alex-ha-192/neo/kicad/buzzers/classic/main/main.kicad_sch

## KiCad design kicad/buzzers/classic/main/main.kicad_sch (2026-09-12)

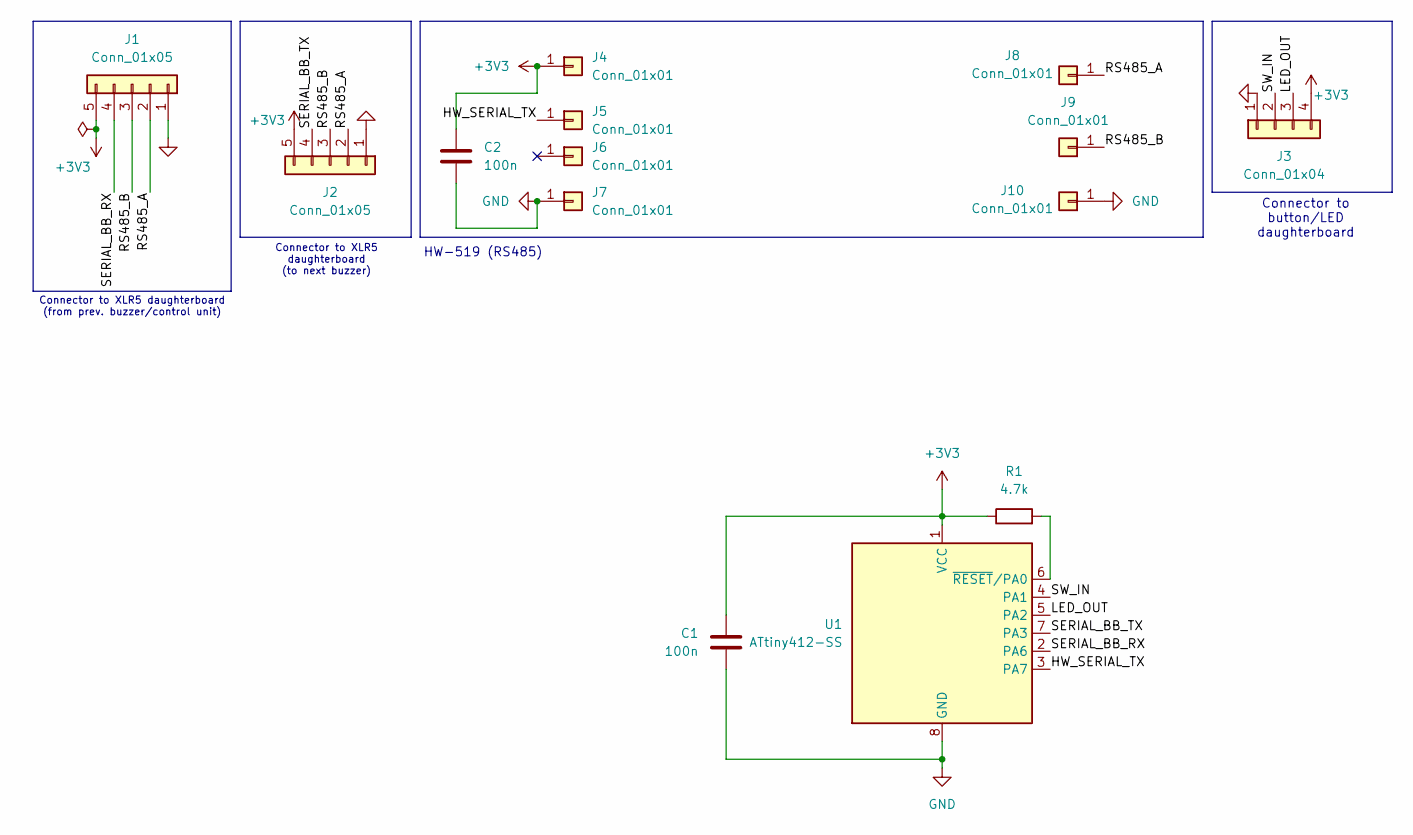
[picture p11: schematic main.kicad_sch]

Parts:
C1, C2: 100n
J1, J2: Conn_01x05
J3: Conn_01x04
J4, J5, J6, J7, J8, J9, J10: Conn_01x01
R1: 4.7k
U1: ATtiny412-SS; SOIC-8_3.9x4.9mm_P1.27mm

Connections:
+3V3: C1.1, C2.1, J1.5, J2.5, J3.4, J4.1, R1.1, U1.1 (VCC)
GND: C1.2, C2.2, J1.1, J2.1, J3.1, J7.1, J10.1, U1.8 (GND)
HW_SERIAL_TX: J5.1, U1.3 (PA7)
LED_OUT: J3.3, U1.5 (PA2)
unnamed: R1.2, U1.6 (~RESET/PA0)
RS485_A: J1.2, J2.2, J8.1
RS485_B: J1.3, J2.3, J9.1
SERIAL_BB_RX: J1.4, U1.2 (PA6)
SERIAL_BB_TX: J2.4, U1.7 (PA3)
SW_IN: J3.2, U1.4 (PA1)

Notes on the sheet:
Connector to button/LED daughterboard
HW-519 (RS485)
Connector to XLR5 daughterboard (from prev. buzzer/control unit)
Connector to XLR5 daughterboard (to next buzzer)
