alex-ha-192/neo/kicad/control_units/classic/led/led.kicad_sch

## KiCad design kicad/control_units/classic/led/led.kicad_sch (2026-06-27)

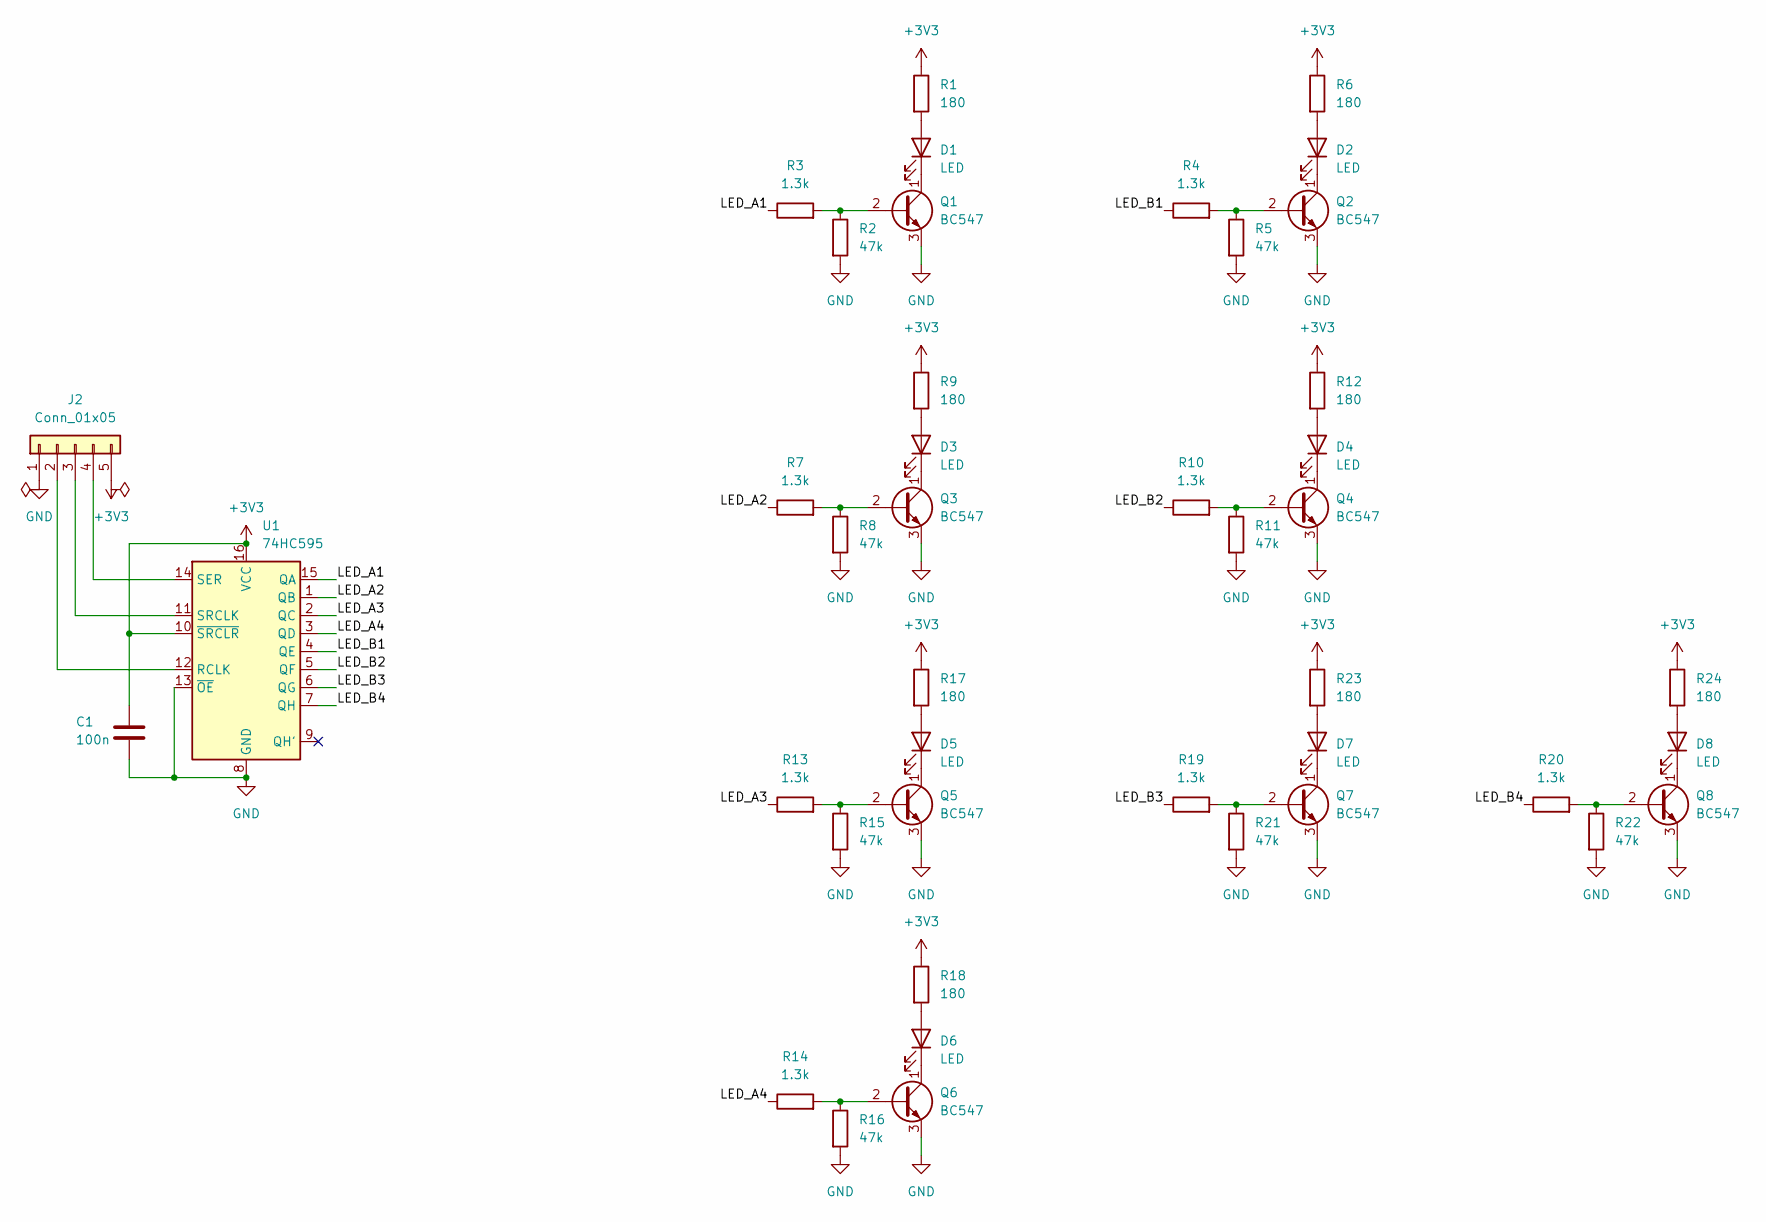
[picture p12: schematic led.kicad_sch]

Parts:
C1: 100n
D1, D2, D3, D4, D5, D6, D7, D8: LED
J2: Conn_01x05
Q1, Q2, Q3, Q4, Q5, Q6, Q7, Q8: BC547; TO-92_Inline
R1, R6, R9, R12, R17, R18, R23, R24: 180
R2, R5, R8, R11, R15, R16, R21, R22: 47k
R3, R4, R7, R10, R13, R14, R19, R20: 1.3k
U1: 74HC595

Connections:
+3V3: C1.1, J2.5, R1.1, R6.1, R9.1, R12.1, R17.1, R18.1, R23.1, R24.1, U1.10 (~SRCLR), U1.16 (VCC)
GND: C1.2, J2.1, Q1.3 (E), Q2.3 (E), Q3.3 (E), Q4.3 (E), Q5.3 (E), Q6.3 (E), Q7.3 (E), Q8.3 (E), R2.2, R5.2, R8.2, R11.2, R15.2, R16.2, R21.2, R22.2, U1.8 (GND), U1.13 (~OE)
LED_A1: R3.1, U1.15 (QA)
LED_A2: R7.1, U1.1 (QB)
LED_A3: R13.1, U1.2 (QC)
LED_A4: R14.1, U1.3 (QD)
LED_B1: R4.1, U1.4 (QE)
LED_B2: R10.1, U1.5 (QF)
LED_B3: R19.1, U1.6 (QG)
LED_B4: R20.1, U1.7 (QH)
unnamed: D1.1 (K), Q1.1 (C)
unnamed: D1.2 (A), R1.2
unnamed: D2.1 (K), Q2.1 (C)
unnamed: D2.2 (A), R6.2
unnamed: D3.1 (K), Q3.1 (C)
unnamed: D3.2 (A), R9.2
unnamed: D4.1 (K), Q4.1 (C)
unnamed: D4.2 (A), R12.2
unnamed: D5.1 (K), Q5.1 (C)
unnamed: D5.2 (A), R17.2
unnamed: D6.1 (K), Q6.1 (C)
unnamed: D6.2 (A), R18.2
unnamed: D7.1 (K), Q7.1 (C)
unnamed: D7.2 (A), R23.2
unnamed: D8.1 (K), Q8.1 (C)
unnamed: D8.2 (A), R24.2
unnamed: J2.2, U1.12 (RCLK)
unnamed: J2.3, U1.11 (SRCLK)
unnamed: J2.4, U1.14 (SER)
unnamed: Q1.2 (B), R2.1, R3.2
unnamed: Q2.2 (B), R4.2, R5.1
unnamed: Q3.2 (B), R7.2, R8.1
unnamed: Q4.2 (B), R10.2, R11.1
unnamed: Q5.2 (B), R13.2, R15.1
unnamed: Q6.2 (B), R14.2, R16.1
unnamed: Q7.2 (B), R19.2, R21.1
unnamed: Q8.2 (B), R20.2, R22.1
