alex-ha-192/neo/kicad/control_units/classic/main/main.kicad_sch

## KiCad design kicad/control_units/classic/main/main.kicad_sch (2026-06-27)

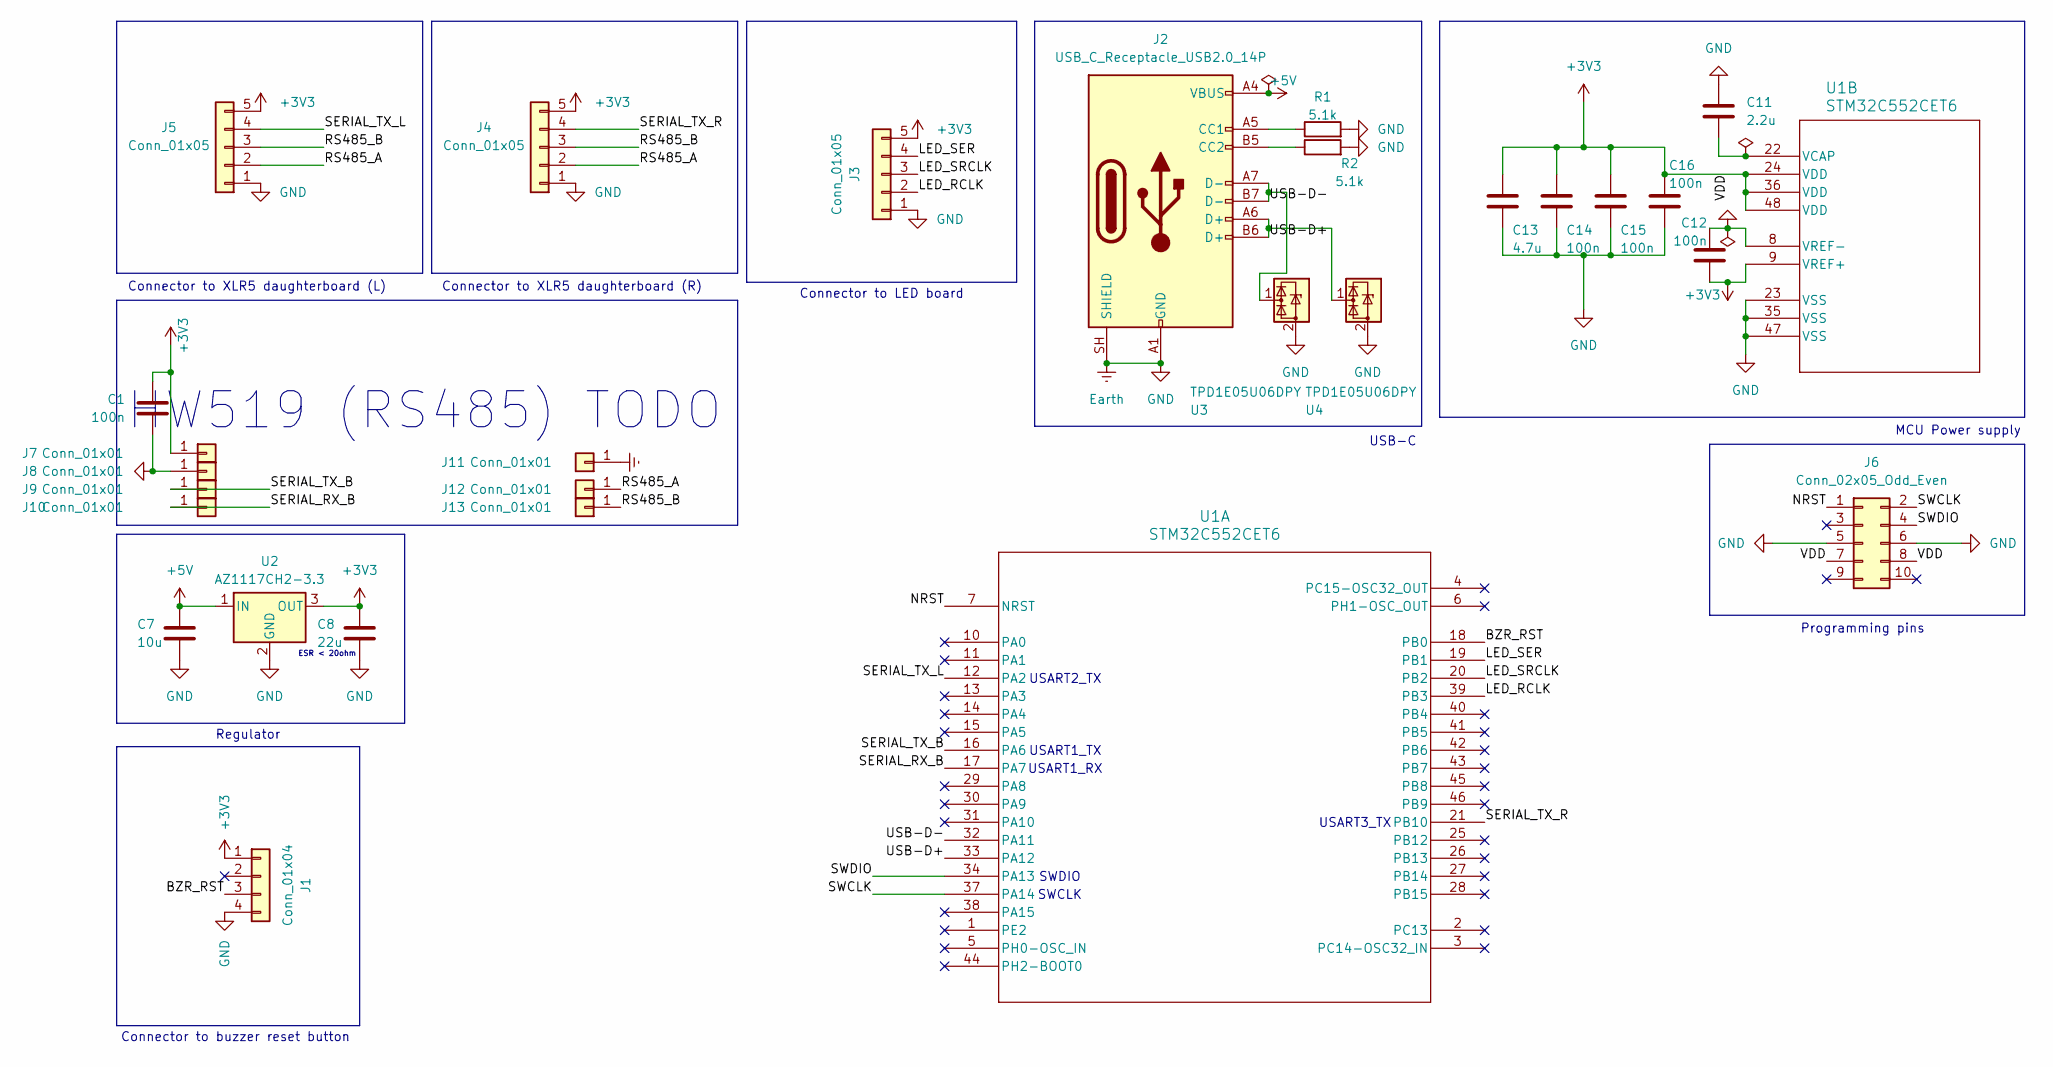
[picture p13: schematic main.kicad_sch]

Parts:
C1: 100n
C7: 10u; C_0805_2012Metric
C8: 22u; C_0805_2012Metric
C11: 2.2u; C_0805_2012Metric
C12, C14, C15, C16: 100n; C_0805_2012Metric
C13: 4.7u; C_0805_2012Metric
J1: Conn_01x04
J2: USB_C_Receptacle_USB2.0_14P; USB_C_Receptacle_Amphenol_12401610E4-2A
J3, J4, J5: Conn_01x05
J6: Conn_02x05_Odd_Even
J7, J8, J9, J10, J11, J12, J13: Conn_01x01
R1, R2: 5.1k; R_0805_2012Metric
U1: STM32C552CET6; LQFP-48_7x7mm_P0.5mm
U2: AZ1117CH2-3.3; SOT-223-3_TabPin2
U3, U4: TPD1E05U06DPY; Texas_DPY0002A_0.6x1mm_P0.65mm

Connections:
+3V3: C1.1, C8.2, C12.1, C13.2, C14.2, C15.2, C16.2, J1.1, J3.5, J4.5, J5.5, J6.7, J6.8, J7.1, U1.9 (VREF+), U1.24 (VDD), U1.36 (VDD), U1.48 (VDD), U2.3 (OUT)
+5V: C7.2, J2.A4 (VBUS), J2.A9 (VBUS), J2.B4 (VBUS), J2.B9 (VBUS), U2.1 (IN)
BZR_RST: J1.3, U1.18 (PB0)
Earth: C1.2, C7.1, C8.1, C11.1, C12.2, C13.1, C14.1, C15.1, C16.1, J1.4, J2.A1 (GND), J2.A12 (GND), J2.B1 (GND), J2.B12 (GND), J2.SH (SHIELD), J3.1, J4.1, J5.1, J6.5, J6.6, J8.1, J11.1, R1.2, R2.2, U1.8 (VREF-), U1.23 (VSS), U1.35 (VSS), U1.47 (VSS), U2.2 (GND), U3.2 (GND), U4.2 (GND)
LED_RCLK: J3.2, U1.39 (PB3)
LED_SER: J3.4, U1.19 (PB1)
LED_SRCLK: J3.3, U1.20 (PB2)
NRST: J6.1, U1.7 (NRST)
unnamed: C11.2, U1.22 (VCAP)
unnamed: J2.A5 (CC1), R1.1
unnamed: J2.B5 (CC2), R2.1
RS485_A: J4.2, J5.2, J12.1
RS485_B: J4.3, J5.3, J13.1
SERIAL_RX_B: J10.1, U1.17 (PA7)
SERIAL_TX_B: J9.1, U1.16 (PA6)
SERIAL_TX_L: J5.4, U1.12 (PA2)
SERIAL_TX_R: J4.4, U1.21 (PB10)
SWCLK: J6.2, U1.37 (PA14)
SWDIO: J6.4, U1.34 (PA13)
USB-D+: J2.A6 (D+), J2.B6 (D+), U1.33 (PA12), U4.1 (I/O)
USB-D-: J2.A7 (D-), J2.B7 (D-), U1.32 (PA11), U3.1 (I/O)

Notes on the sheet:
USB-C
Connector to XLR5 daughterboard (R)
Connector to buzzer reset button
ESR < 20ohm
USART2_TX
Regulator
USART1_TX
Programming pins
SWDIO
MCU Power supply
Connector to LED board
Connector to XLR5 daughterboard (L)
SWCLK
USART3_TX
USART1_RX
HW519 (RS485) TODO
